VictorI76/InkTime/Images/InkTime_PCB_2.png

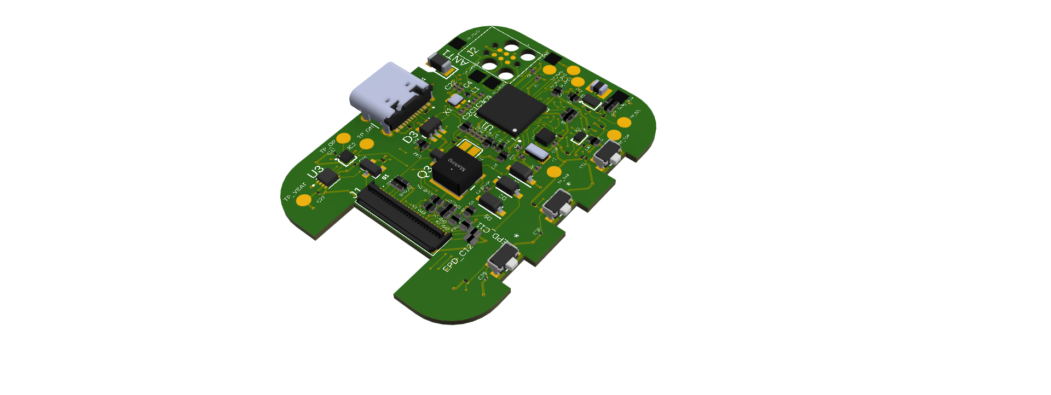
Images/InkTime_PCB_2.png
