VictorI76/InkTime/Images/InkTime_PCB_Bottom.png

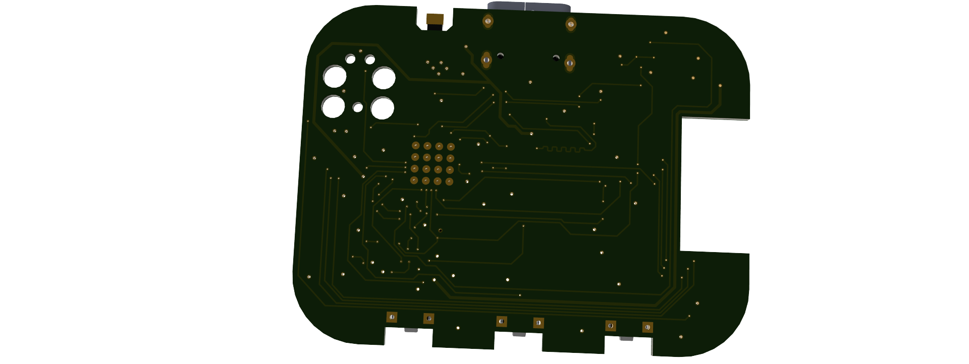
Images/InkTime_PCB_Bottom.png
